Souza04Gustavo/ic_craniometer_udesc/media/photo_2.jpg

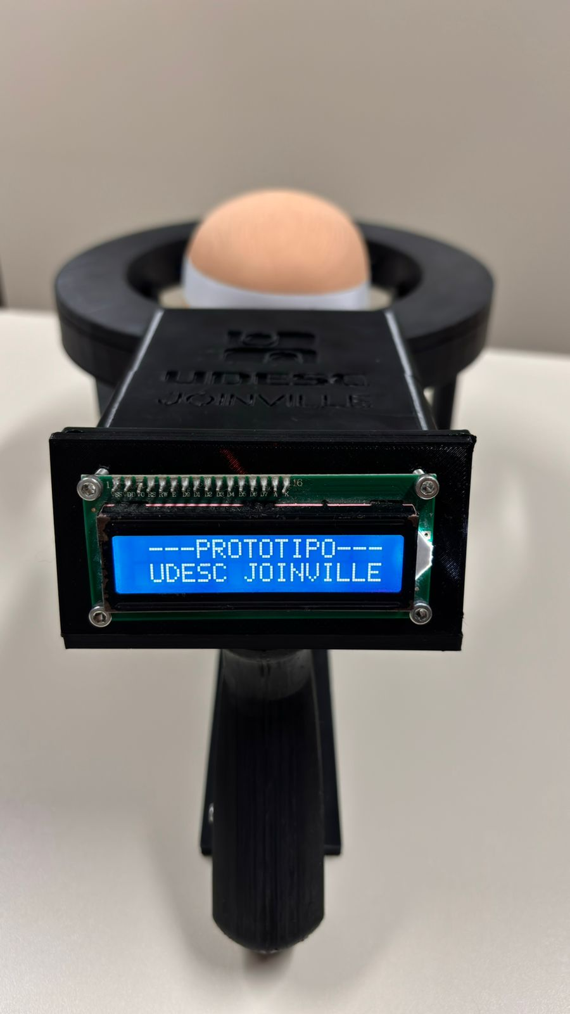
media/photo_2.jpg
