Souza04Gustavo/ic_craniometer_udesc/media/photo_3.jpg

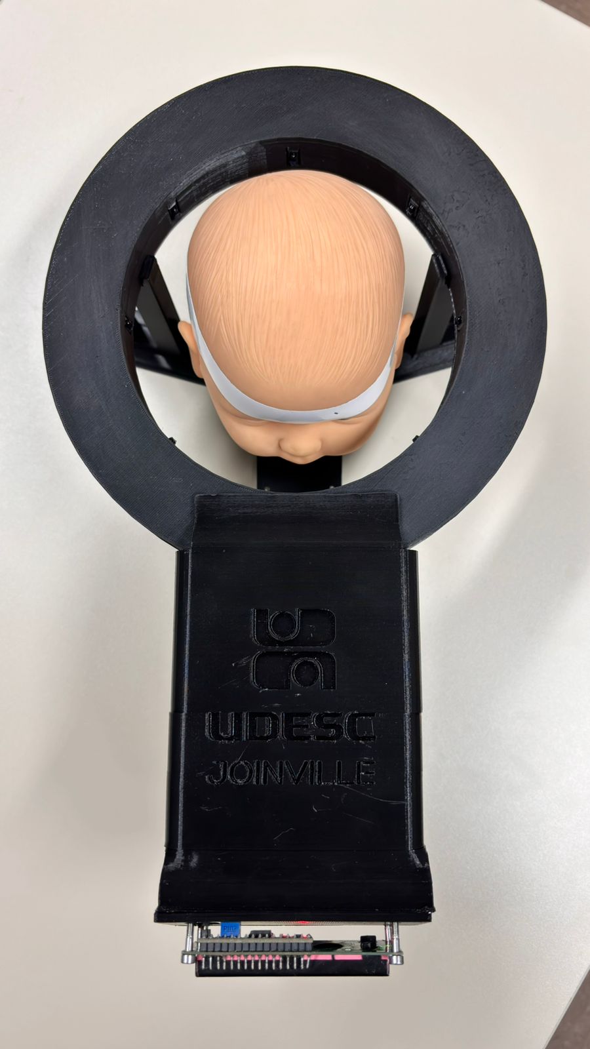
media/photo_3.jpg
