Souza04Gustavo/ic_craniometer_udesc/media/photo_4.jpg

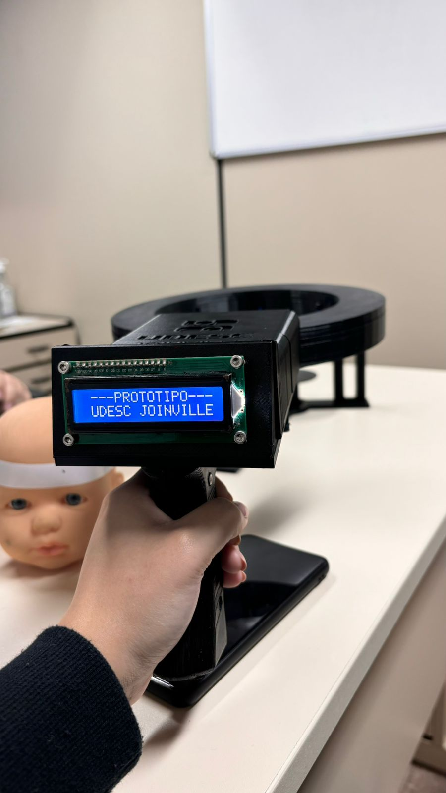
media/photo_4.jpg
