Souza04Gustavo/ic_craniometer_udesc/3D_parts_STL/tampa_principal_com_udesc_v2.stl

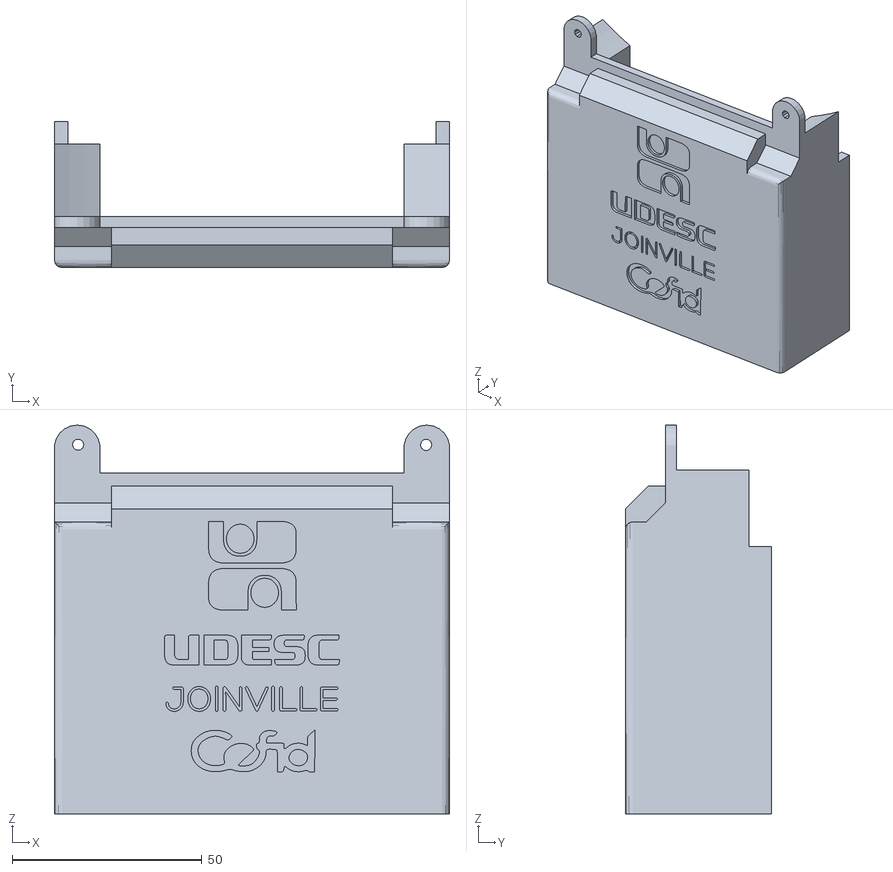
[picture p25: CAD file, 2025-03-11]
3D_parts_STL/tampa_principal_com_udesc_v2.stl
104.0 x 38.5 x 102.4
