Souza04Gustavo/ic_craniometer_udesc/3D_parts_STL/empunhadura_fatiada.stl

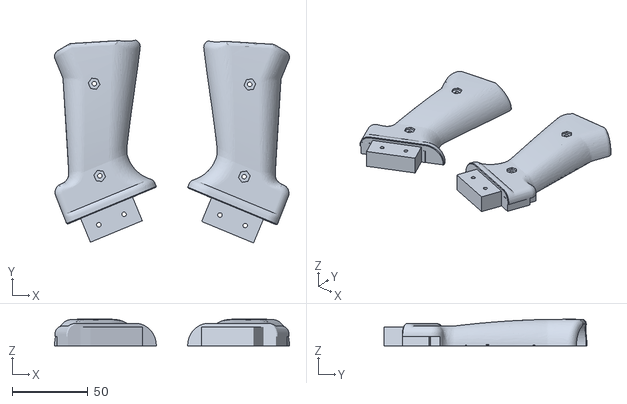
[picture p26: CAD file, 2025-03-11]
3D_parts_STL/empunhadura_fatiada.stl
154.7 x 133.6 x 17.5
