Souza04Gustavo/ic_craniometer_udesc/3D_parts_STL/calibrador(1,0cm).stl

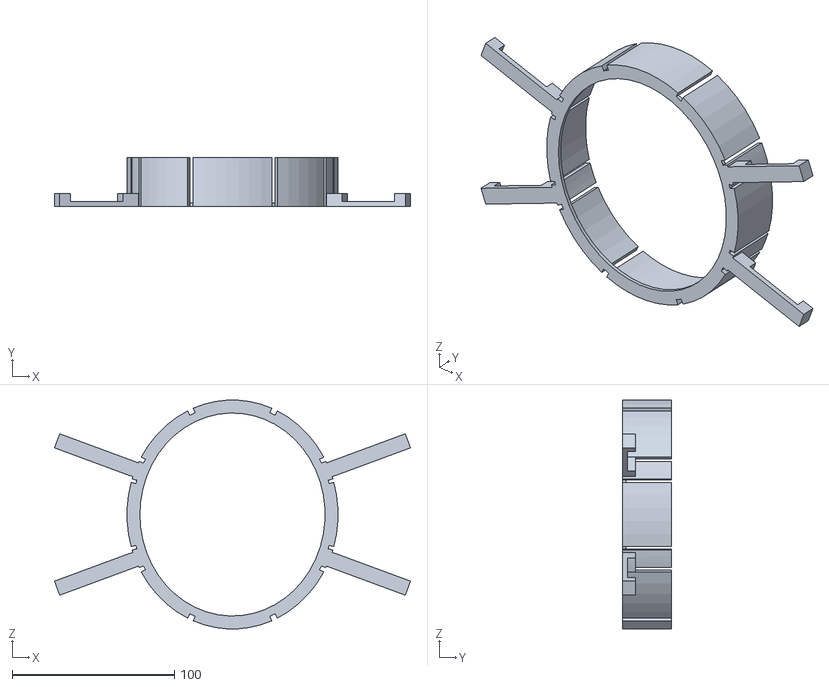
[picture p27: CAD file, 2025-03-11]
3D_parts_STL/calibrador(1,0cm).stl
219.2 x 30.0 x 140.8
