Souza04Gustavo/ic_craniometer_udesc/3D_parts_STL/tampa_SEM_UDESC_JOINVILLE.stl

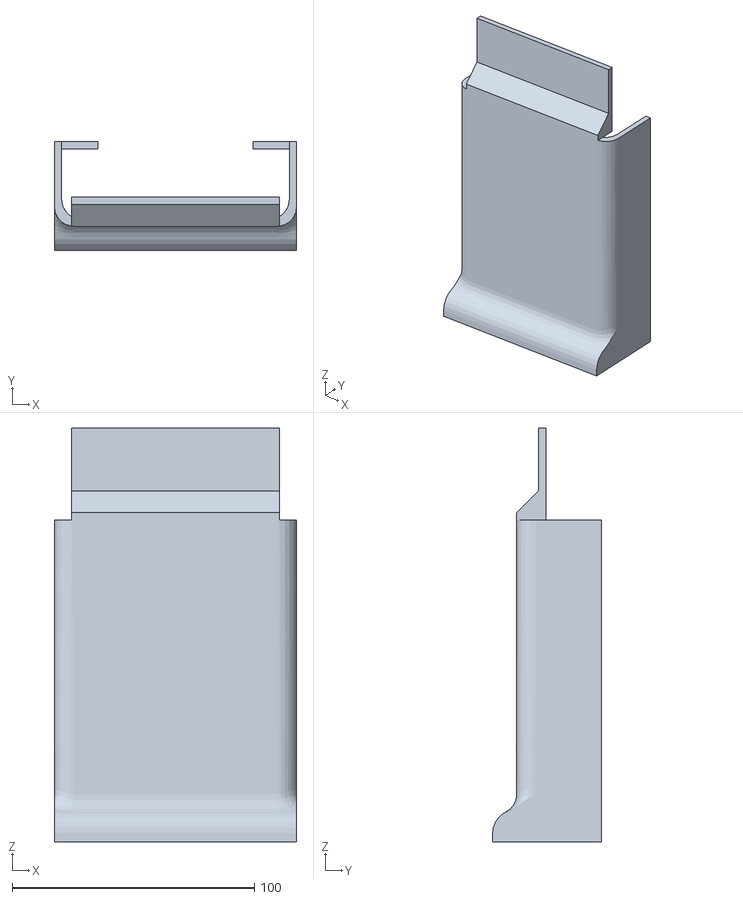
[picture p28: CAD file, 2025-03-11]
3D_parts_STL/tampa_SEM_UDESC_JOINVILLE.stl
100.0 x 45.0 x 171.0
