Souza04Gustavo/ic_craniometer_udesc/3D_parts_STL/tampa_anel.stl

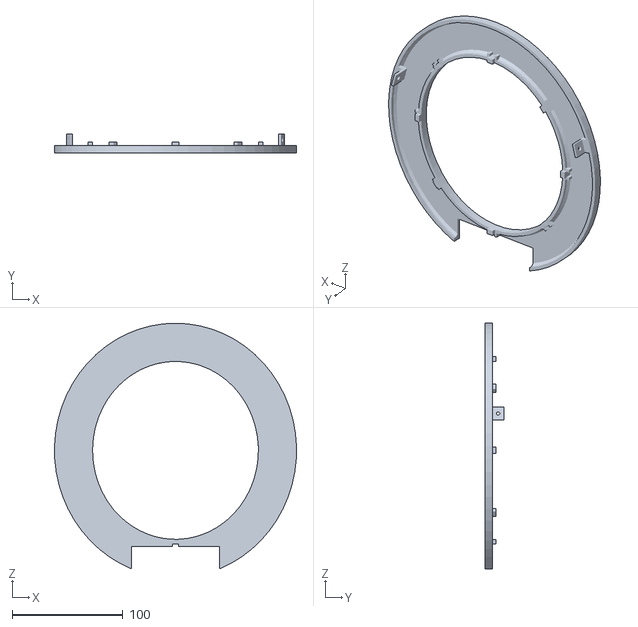
[picture p29: CAD file, 2025-03-11]
3D_parts_STL/tampa_anel.stl
218.9 x 17.5 x 222.1
