Souza04Gustavo/ic_craniometer_udesc/scripts/componentes_testes/mpuJuntoLiquidCrystal/mpuJuntoLiquidCrystal.ino

#include <Adafruit_MPU6050.h>
#include <Adafruit_Sensor.h>
#include <Wire.h>
#include <LiquidCrystal_I2C.h>

Adafruit_MPU6050 mpu;

#define col 16
#define lin  2
#define ende  0x27

LiquidCrystal_I2C lcd(ende,col,lin);

void setup(void) {
  
  Serial.begin(115200);

  lcd.init(); // Serve para iniciar a comunicação com o display já conectado
  lcd.backlight(); // Serve para ligar a luz do display
  lcd.clear(); // Serve para limpar a tela do display

  while (!Serial)
    delay(10); // will pause Zero, Leonardo, etc until serial console opens

  Serial.println("Adafruit MPU6050 test!");

  // Try to initialize!
  if (!mpu.begin()) {
    Serial.println("Failed to find MPU6050 chip");
    while (1) {
      delay(10);
    }
  }
  Serial.println("MPU6050 Found!");

  mpu.setAccelerometerRange(MPU6050_RANGE_8_G);
  /*
  Serial.print("Accelerometer range set to: ");
  switch (mpu.getAccelerometerRange()) {
  case MPU6050_RANGE_2_G:
    Serial.println("+-2G");
    break;
  case MPU6050_RANGE_4_G:
    Serial.println("+-4G");
    break;
  case MPU6050_RANGE_8_G:
    Serial.println("+-8G");
    break;
  case MPU6050_RANGE_16_G:
    Serial.println("+-16G");
    break;
  }
*/

  mpu.setGyroRange(MPU6050_RANGE_500_DEG);
  /*
  Serial.print("Gyro range set to: ");
  switch (mpu.getGyroRange()) {
  case MPU6050_RANGE_250_DEG:
    Serial.println("+- 250 deg/s");
    break;
  case MPU6050_RANGE_500_DEG:
    Serial.println("+- 500 deg/s");
    break;
  case MPU6050_RANGE_1000_DEG:
    Serial.println("+- 1000 deg/s");
    break;
  case MPU6050_RANGE_2000_DEG:
    Serial.println("+- 2000 deg/s");
    break;
  }
  */

  mpu.setFilterBandwidth(MPU6050_BAND_21_HZ);
  /*
  Serial.print("Filter bandwidth set to: ");
  switch (mpu.getFilterBandwidth()) {
  case MPU6050_BAND_260_HZ:
    Serial.println("260 Hz");
    break;
  case MPU6050_BAND_184_HZ:
    Serial.println("184 Hz");
    break;
  case MPU6050_BAND_94_HZ:
    Serial.println("94 Hz");
    break;
  case MPU6050_BAND_44_HZ:
    Serial.println("44 Hz");
    break;
  case MPU6050_BAND_21_HZ:
    Serial.println("21 Hz");
    break;
  case MPU6050_BAND_10_HZ:
    Serial.println("10 Hz");
    break;
  case MPU6050_BAND_5_HZ:
    Serial.println("5 Hz");
    break;
  }
  */

  Serial.println("");
  delay(100);
}

void loop() {

  lcd.setCursor(1,0); // Coloca o cursor do display na coluna 1 e linha 1
  lcd.print("VIVA O YURI"); // Comando de saída com a mensagem que deve aparecer na coluna 2 e linha 1.
  
  //lcd.clear(); // Limpa o display até o loop ser reiniciado 

  /* Get new sensor events with the readings */
  sensors_event_t a, g, temp;
  mpu.getEvent(&a, &g, &temp);

  /* Print out the values */

  /*
  Serial.print("Acceleration X: ");
  Serial.print(a.acceleration.x);
  Serial.print(", Y: ");
  Serial.print(a.acceleration.y);
  Serial.print(", Z: ");
  Serial.print(a.acceleration.z);
  Serial.println(" m/s^2");
*/



//  Serial.print("Rotation X: ");
Serial.print(10);
   Serial.print(" ");
  Serial.print(g.gyro.x);
  Serial.print(" ");
//  Serial.print(", Y: ");
  Serial.print(g.gyro.y);
  Serial.print(" ");
//  Serial.print(", Z: ");
  Serial.print(g.gyro.z);
  Serial.print(" ");
  Serial.print(-10);
//  Serial.println(" rad/s");


Serial.println("");
  delay(10);
}
